DansDesigns/Scicorder-mini/UST_v01a/about.ino

/*
 *    
   FDTI: COM14
   DevBoard: COM15

   Settings for Arduino IDE:
   BOARD:           ESP32-WROOM-(32)DA
   UPLOAD SPEED:    921600
   CPU FREQ:        240mhz
   FLASH SIZE:      4mb(Default)
   FLASH MODE:      QIO
   PARTITION:       Default
  
  
   Sketch uses 1195781 bytes (60%) of program storage space. Maximum is 1966080 bytes.
   Global variables use 55444 bytes (16%) of dynamic memory, leaving 272236 bytes for local variables. Maximum is 327680 bytes.

 */
